timblakely/pino-rs/notes/robotics.md

# Actuation

## TELLO leg

[Interesting hip ab/ad mechanism](https://www.youtube.com/watch?v=62lo04Up2vc)
