timblakely/pino-rs/notes/references/motors.md

# Motor control

- [TI application report](https://www.ti.com/lit/an/sboa172/sboa172.pdf?ts=1628044378998) on
  "Current Sensing for Inline Motor-Control Applications"
  - Common gotchas on current sensing
- [Falstad
  simulation](https://www.falstad.com/circuit/circuitjs.html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)
  of current through a winding
- [Slides](http://www.kappaiq.com/download/presentation-material/PDF/03%20Field%20Oriented%20Control.pdf)
  from [Teaching Old Motors New Tricks](https://www.youtube.com/watch?v=VI7pdKrchM0) series
