timblakely/pino-rs/notes/control theory bootcamp/part38.md

# Part 38 - [Control Systems with Non-Minimum Phase Dynamics](https://www.youtube.com/watch?v=7GjnvuKeWI8&list=PLMrJAkhIeNNR20Mz-VpzgfQs5zrYi085m&index=38)

Non-minimum phase: hard to control
1. Right-half plane zero (in transfer function)
  - $G(s)=\frac{\bar{y}(s)}{\bar{u}(s)}=\frac{s-1}{s+10}$

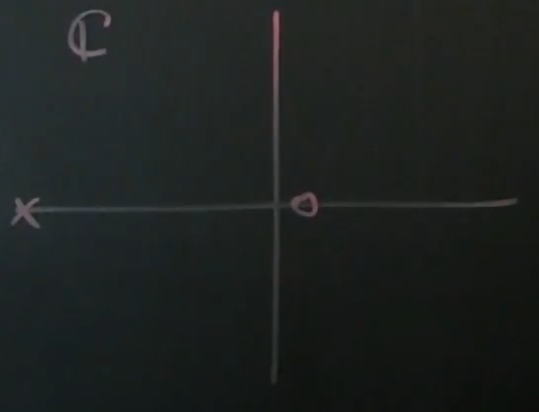
[picture p2: notes/control theory bootcamp/images/2021-08-30-21-44-45.png]
    

  - Stable because pole is in left half of plane
  - Zero is at +1
2. Impulse response "goes in the wrong direction" first

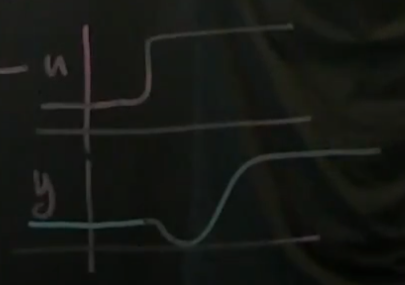
[picture p3: notes/control theory bootcamp/images/2021-08-30-21-46-07.png]
  

  - Implies 1 above
