timblakely/pino-rs/notes/control theory bootcamp/part35.md

# Part 35 - [Sensitivity and Robustness](https://www.youtube.com/watch?v=7lzH-HnUFZg&list=PLMrJAkhIeNNR20Mz-VpzgfQs5zrYi085m&index=35)

Recap:
$L=PK$

$S=\left(I+L\right)^{-1}$

$T=\left(I+L\right)^{-1}L$

Background:
- Nyquist stability criteria
  - Idea: want loop transfer function $L$ to be as far away from the point $-1$ in the complex plane for _all_ frequencies

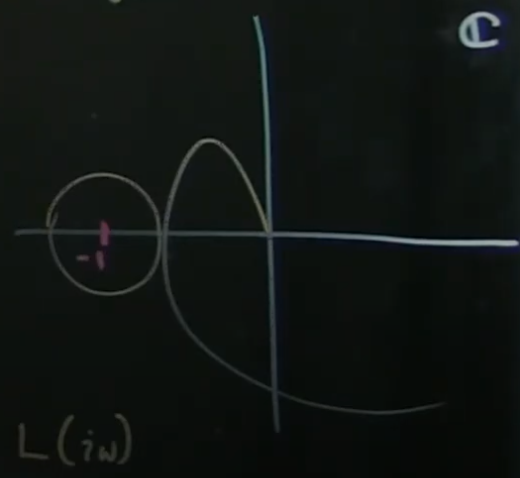
[picture p7: notes/control theory bootcamp/images/2021-08-30-20-00-49.png]
  

    - Closer it gets to -1, the less robust a system is
    - Min distance from -1 (radius) is "robustness"
  - Changes in $P$ and $K$ make curve grow/shrink from -1
    - Increasing model uncertainty $P$ and/or increased gains $K$
  - Phase changes make transfer function rotate bout origin
    - Time delays during dynamics change phase

Why is -1 so special?

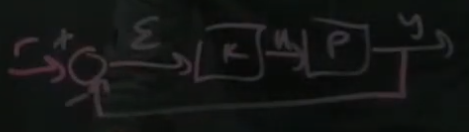
[picture p8: notes/control theory bootcamp/images/2021-08-30-20-01-43.png]
  
  - $y=\frac{PK}{1+PK}r$
  - If $PK=-1$, system blows up

$S=\frac{1}{1+L}$
- Closer $L$ is to -1, $S$ becomes big
- $max\left|S\right|$ at $\omega$

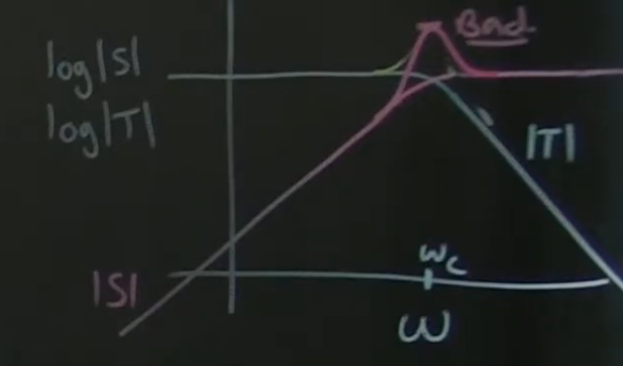
[picture p9: notes/control theory bootcamp/images/2021-08-30-20-09-06.png]
