timblakely/pino-rs/notes/control theory bootcamp/part23.md

# Part 23 - [LQG example in matlab](https://www.youtube.com/watch?v=reRT8LbPhBs&list=PLMrJAkhIeNNR20Mz-VpzgfQs5zrYi085m&index=23)

More matlab cart-poles

Initial cart model:

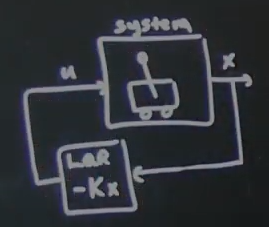
[picture p34: notes/control theory bootcamp/images/2021-08-25-15-04-42.png]


Going to plug in LQE
- Stabilizing around $\begin{bmatrix}x\\ \dot{x} \\ \theta \\ \dot{\theta}\end{bmatrix}=\begin{bmatrix}0\\0\\ \pi \\0\end{bmatrix}$

Implementation in simulink
