timblakely/pino-rs/notes/contol systems lectures/images/2021-08-14-22-57-17.png

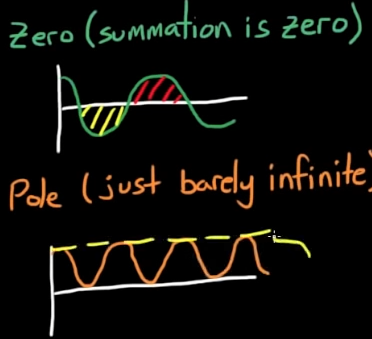
notes/contol systems lectures/images/2021-08-14-22-57-17.png
