timblakely/pino-rs/notes/control theory bootcamp/images/2021-06-19-16-52-32.png

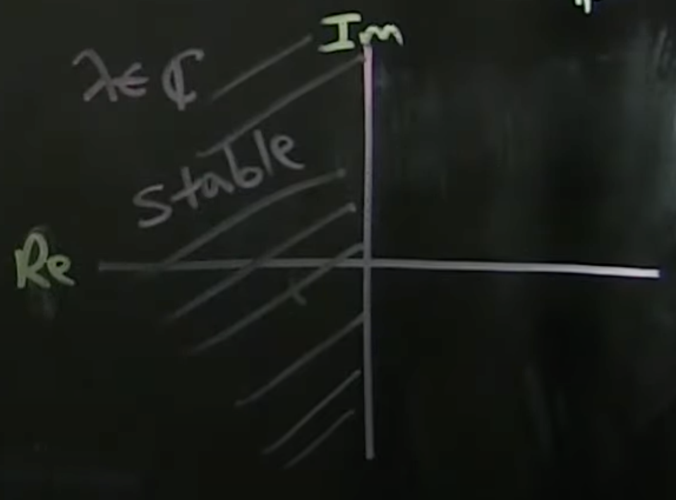
notes/control theory bootcamp/images/2021-06-19-16-52-32.png
