timblakely/pino-rs/notes/control theory bootcamp/images/2021-08-24-16-37-29.png

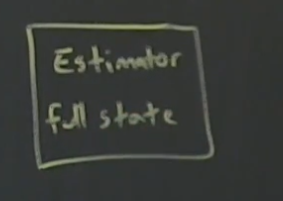
notes/control theory bootcamp/images/2021-08-24-16-37-29.png
