timblakely/pino-rs/notes/control theory bootcamp/images/2021-08-25-19-04-28.png

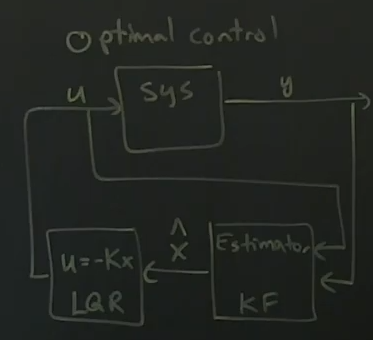
notes/control theory bootcamp/images/2021-08-25-19-04-28.png
