timblakely/pino-rs/notes/control theory bootcamp/images/2021-08-28-13-41-20.png

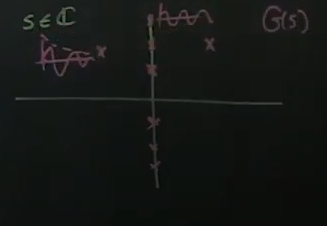
notes/control theory bootcamp/images/2021-08-28-13-41-20.png
