timblakely/pino-rs/notes/control theory bootcamp/images/2021-08-28-21-21-02.png

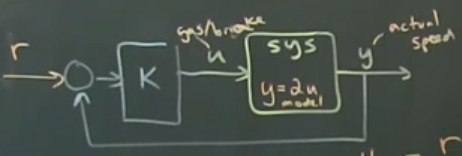
notes/control theory bootcamp/images/2021-08-28-21-21-02.png
