timblakely/pino-rs/notes/control theory bootcamp/images/2021-08-29-13-17-43.png

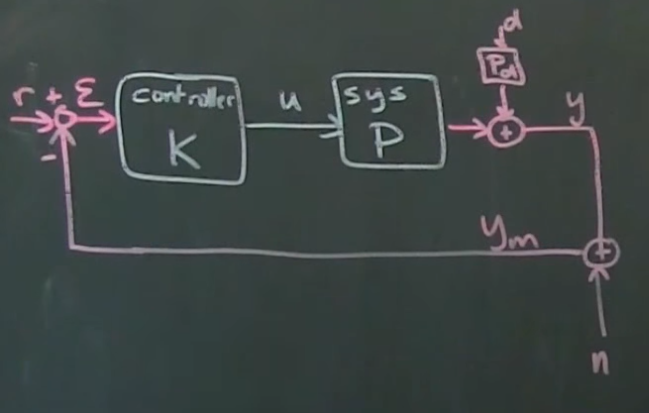
notes/control theory bootcamp/images/2021-08-29-13-17-43.png
