timblakely/pino-rs/notes/control theory bootcamp/images/2021-08-30-19-57-59.png

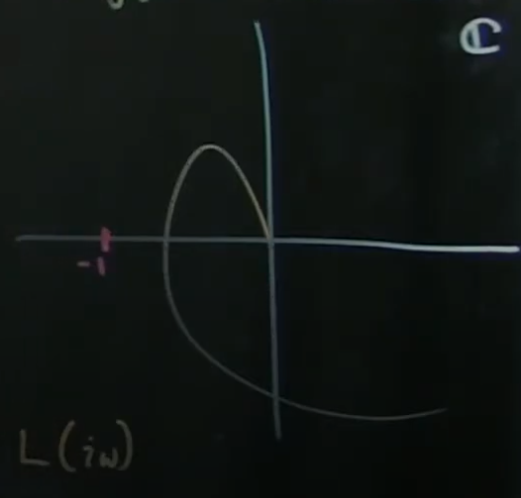
notes/control theory bootcamp/images/2021-08-30-19-57-59.png
