timblakely/pino-rs/notes/devlog/images/2021-07-29-00-01-32.png

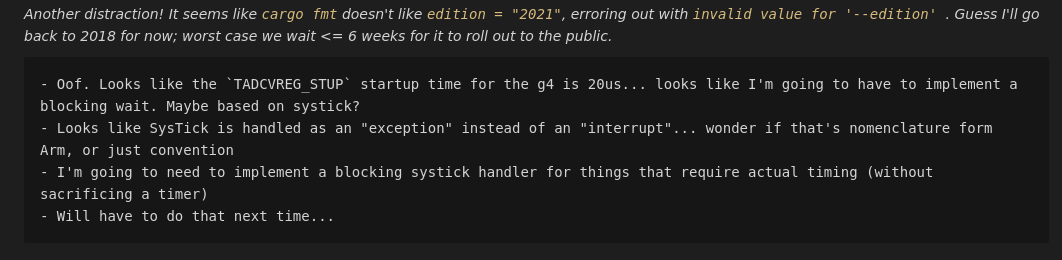
notes/devlog/images/2021-07-29-00-01-32.png
