timblakely/pino-rs/notes/devlog/images/2021-08-17-20-05-19.png

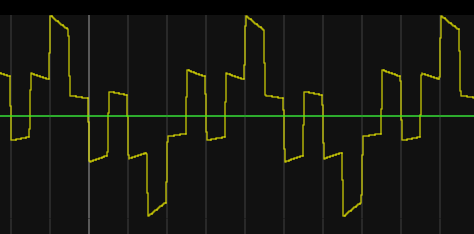
notes/devlog/images/2021-08-17-20-05-19.png
