timblakely/pino-rs/notes/devlog/images/2021-08-20-22-21-41.png

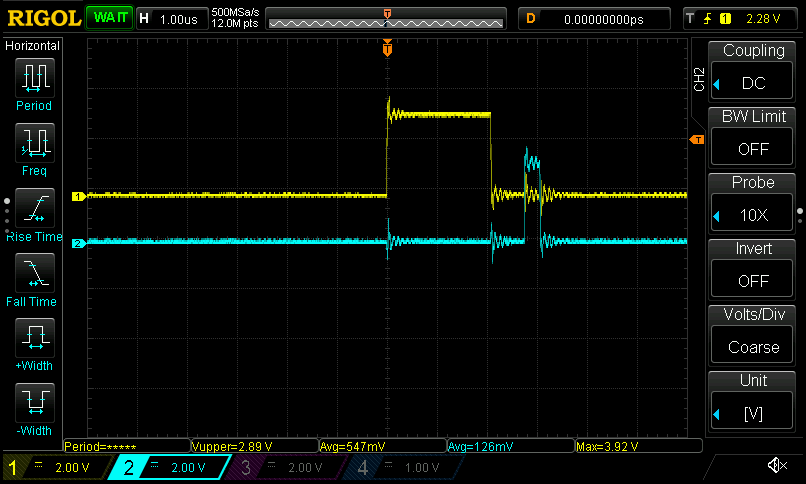
notes/devlog/images/2021-08-20-22-21-41.png
