timblakely/pino-rs/notes/devlog/images/2021-08-26-13-26-06.png

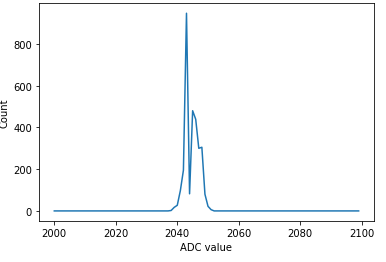
notes/devlog/images/2021-08-26-13-26-06.png
