timblakely/pino-rs/bldc/src/control_loops/idle_current_distribution.rs

use super::{Commutate, ControlHardware, LoopState, SensorState};
use crate::comms::fdcan::{FdcanMessage, IncomingFdcanFrame, OutgoingFdcanFrame};

// Sample current one one phase for a period of time, building a histogram of currents.

// Build a 16-bin distribution of current, one phase at a time.
pub struct IdleCurrentDistributionCmd {
    pub duration: f32,
    pub center_current: f32,
    pub current_range: f32,
    pub phase: u8,
}

// Response to IdleCurrentDistributionCmd
pub struct CurrentDistribution<'a> {
    pub bins: &'a [u32; 16],
}

enum Phase {
    A,
    B,
    C,
}

pub struct IdleCurrentDistribution {
    total_counts: u32,
    loop_count: u32,
    bins: [u32; 16],
    current_min: f32,
    current_binsize: f32,
    phase: Phase,
    callback: for<'r> fn(&'r [u32; 16]),
}

impl IdleCurrentDistribution {
    pub fn new(
        duration: f32,
        center: f32,
        range: f32,
        phase: u8,
        callback: for<'r> fn(&'r [u32; 16]),
    ) -> IdleCurrentDistribution {
        let current_min = center - range;
        let current_binsize = range * 2. / 16.;
        let phase = match phase {
            0 => Phase::A,
            1 => Phase::B,
            _ => Phase::C,
        };
        IdleCurrentDistribution {
            total_counts: (40_000 as f32 * duration) as u32,
            loop_count: 0,
            bins: [0; 16],
            current_min,
            current_binsize,
            phase,
            callback,
        }
    }
}

impl Commutate for IdleCurrentDistribution {
    fn commutate(
        &mut self,
        _loop_state: LoopState,
        _sensor_state: &SensorState,
        hardware: &mut ControlHardware,
    ) -> LoopState {
        self.loop_count += 1;
        let current_sensor = &hardware.current_sensor;
        let sample = current_sensor.sample();

        let current_value = match self.phase {
            Phase::A => sample.phase_a,
            Phase::B => sample.phase_b,
            Phase::C => sample.phase_c,
        };

        let bin_index = ((current_value - self.current_min) / self.current_binsize) as usize;
        let bin_index = bin_index.max(0).min(self.bins.len() - 1);
        self.bins[bin_index] += 1;

        match self.loop_count {
            x if x >= self.total_counts => LoopState::Idle,
            _ => LoopState::Running,
        }
    }

    fn finished(&mut self) {
        (self.callback)(&self.bins);
    }
}

impl IncomingFdcanFrame for IdleCurrentDistributionCmd {
    fn unpack(message: FdcanMessage) -> Self {
        let buffer = message.data;
        IdleCurrentDistributionCmd {
            duration: f32::from_bits(buffer[0]),
            center_current: f32::from_bits(buffer[1]),
            current_range: f32::from_bits(buffer[2]),
            phase: buffer[3] as u8 & 0xFF,
        }
    }
}

impl<'a> OutgoingFdcanFrame for CurrentDistribution<'a> {
    fn pack(&self) -> FdcanMessage {
        FdcanMessage::new(0x10, self.bins)
    }
}
