timblakely/pino-rs/bldc/src/control_loops/calibrate_adc.rs

use crate::{
    comms::fdcan::{FdcanMessage, IncomingFdcanFrame},
    current_sensing::PhaseCurrents,
};

use super::{Commutate, ControlHardware, LoopState, SensorState};

// Calibrate ADC values.
pub struct CalibrateADCCmd {
    pub duration: f32,
}

pub struct CalibrateADC {
    total_counts: u32,
    loop_count: u32,
    sample: PhaseCurrents,
    callback: for<'r> fn(&'r PhaseCurrents),
}

impl CalibrateADC {
    pub fn new(duration: f32, callback: for<'r> fn(&'r PhaseCurrents)) -> CalibrateADC {
        CalibrateADC {
            total_counts: (40_000 as f32 * duration) as u32,
            loop_count: 0,
            sample: PhaseCurrents::new(),
            callback,
        }
    }
}

impl Commutate for CalibrateADC {
    fn commutate(
        &mut self,
        _loop_state: LoopState,
        _sensor_state: &SensorState,
        hardware: &mut ControlHardware,
    ) -> LoopState {
        self.loop_count += 1;
        let current_sensor = &mut hardware.current_sensor;
        self.sample += current_sensor.sample_raw();

        match self.loop_count {
            x if x >= self.total_counts => {
                self.sample /= self.loop_count;
                current_sensor.set_calibration(
                    self.sample.phase_a,
                    self.sample.phase_b,
                    self.sample.phase_c,
                );
                LoopState::Idle
            }
            _ => LoopState::Running,
        }
    }

    fn finished(&mut self) {
        (self.callback)(&self.sample);
    }
}

impl IncomingFdcanFrame for CalibrateADCCmd {
    fn unpack(message: FdcanMessage) -> Self {
        let buffer = message.data;
        CalibrateADCCmd {
            duration: f32::from_bits(buffer[0]),
        }
    }
}
